KushlaVR/models-heart/Firmware/dev-server/App_Data/html/img/bg.jpg

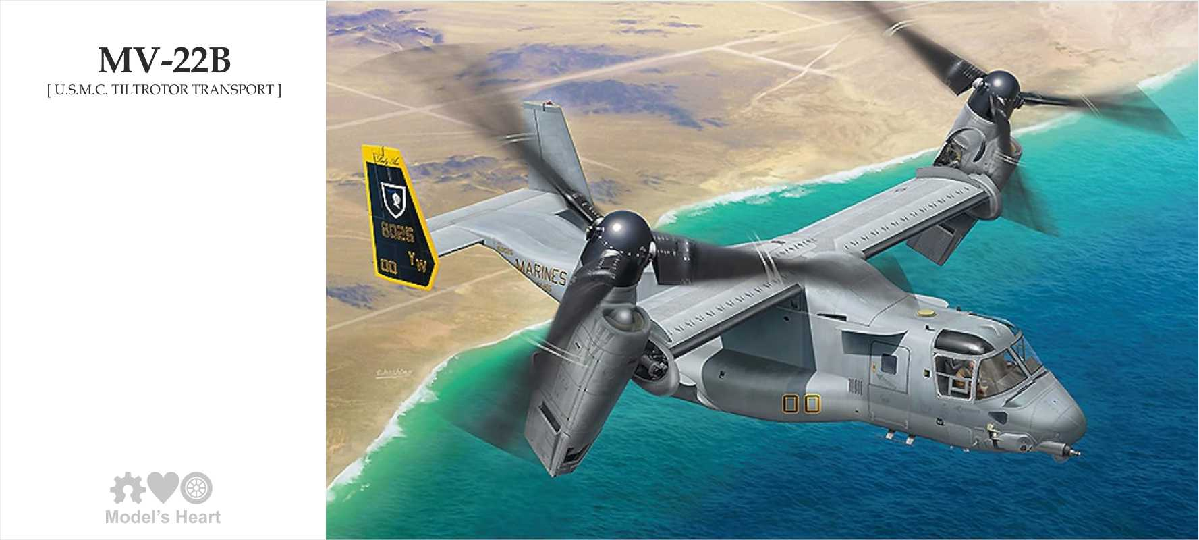
Firmware/dev-server/App_Data/html/img/bg.jpg
