KushlaVR/models-heart/img/3D-rev2-top.png

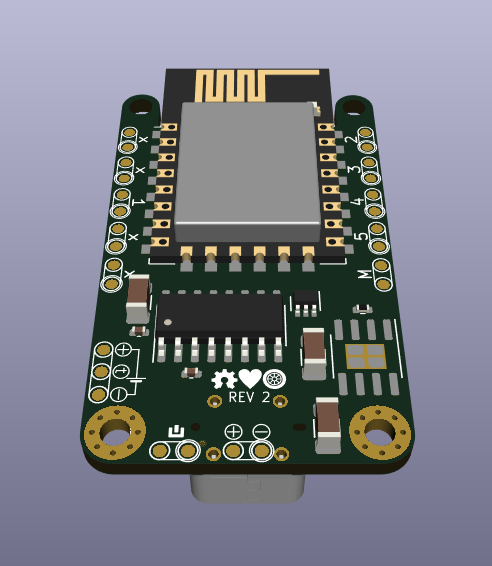
img/3D-rev2-top.png
