KushlaVR/models-heart/img/3D-rev2.png

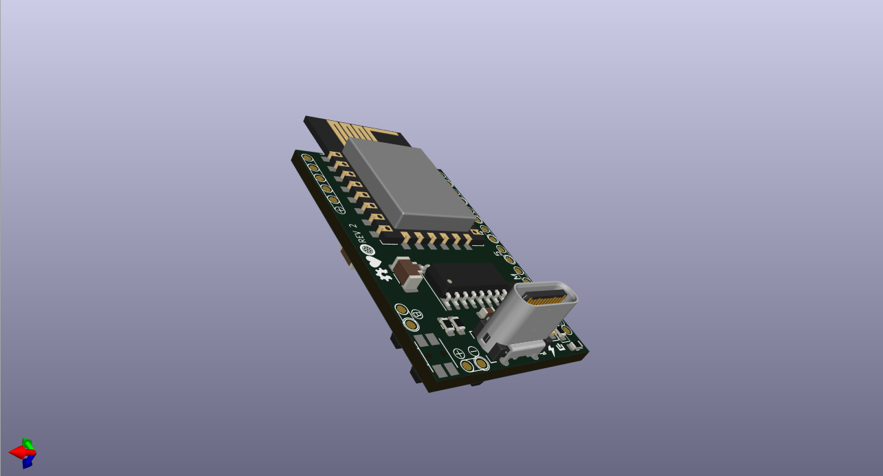
img/3D-rev2.png
