KushlaVR/models-heart/img/3D.png

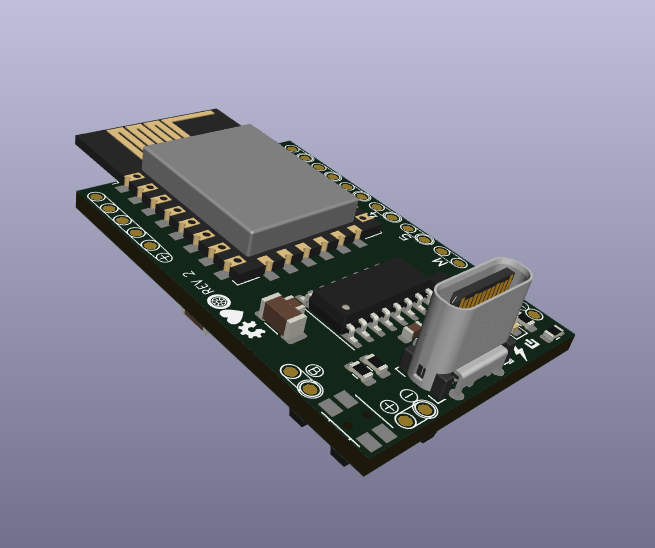
img/3D.png
