KushlaVR/models-heart/PCB/models-heart.png

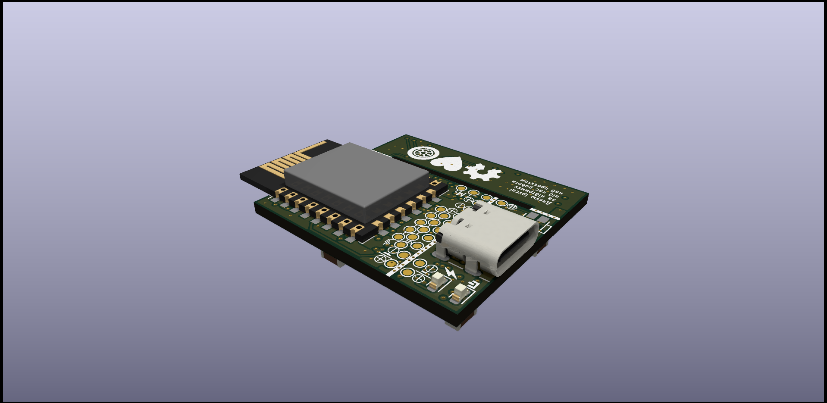
PCB/models-heart.png
